mai-array/UC2-Custom-Build-for-Fluorescence-In-Incubator-Imaging/Diagrams/LightPath.jpg

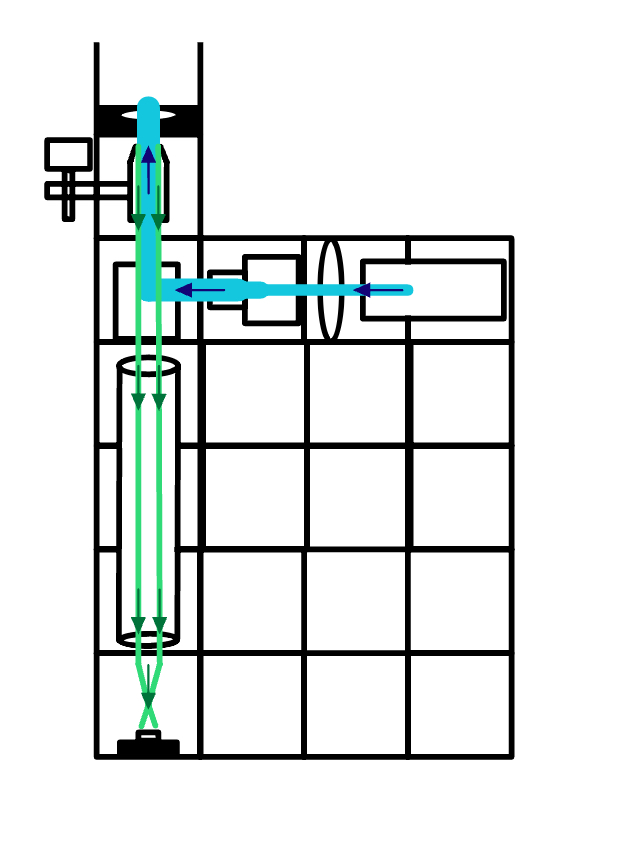
Diagrams/LightPath.jpg
