mai-array/UC2-Custom-Build-for-Fluorescence-In-Incubator-Imaging/Image Collections/Data Collection 1/auto_2025-11-21_13-37-24.jpg

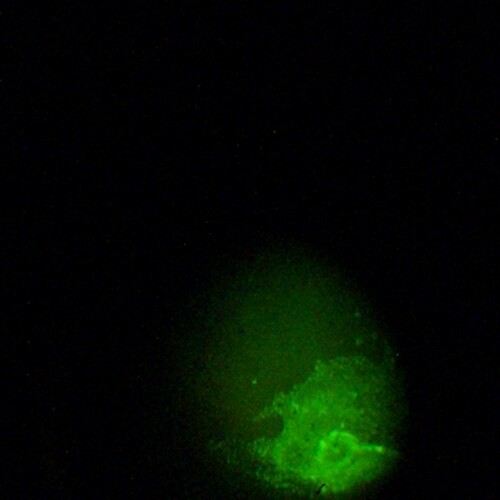
Image Collections/Data Collection 1/auto_2025-11-21_13-37-24.jpg
