mai-array/UC2-Custom-Build-for-Fluorescence-In-Incubator-Imaging/Module Pictures/beamexpander.jpg

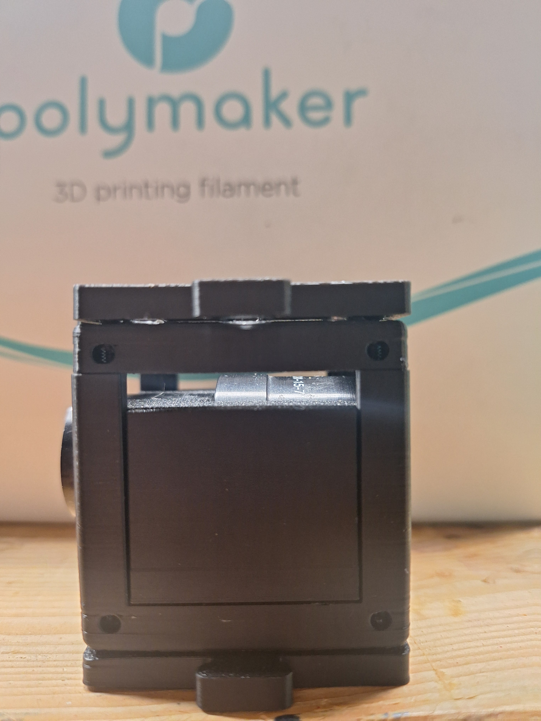
Module Pictures/beamexpander.jpg
