mai-array/UC2-Custom-Build-for-Fluorescence-In-Incubator-Imaging/Module Pictures/dichroic_beamsplitter.jpg

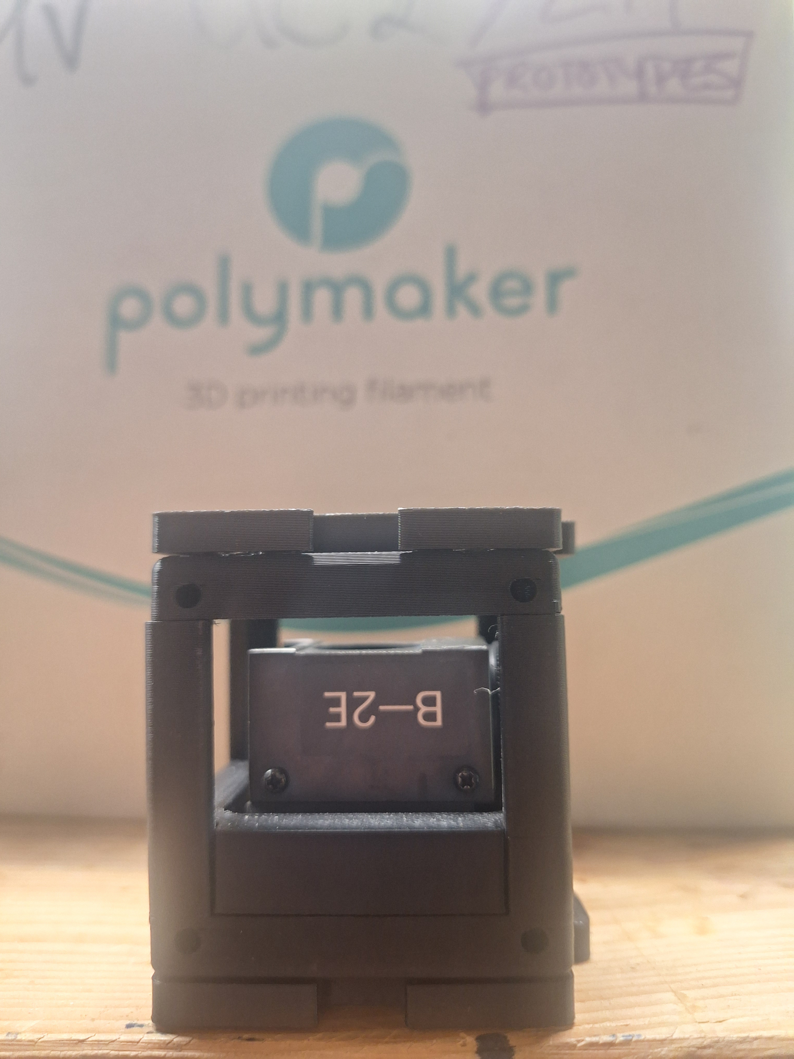
Module Pictures/dichroic_beamsplitter.jpg
