mai-array/UC2-Custom-Build-for-Fluorescence-In-Incubator-Imaging/Module Pictures/nd_filter.jpg

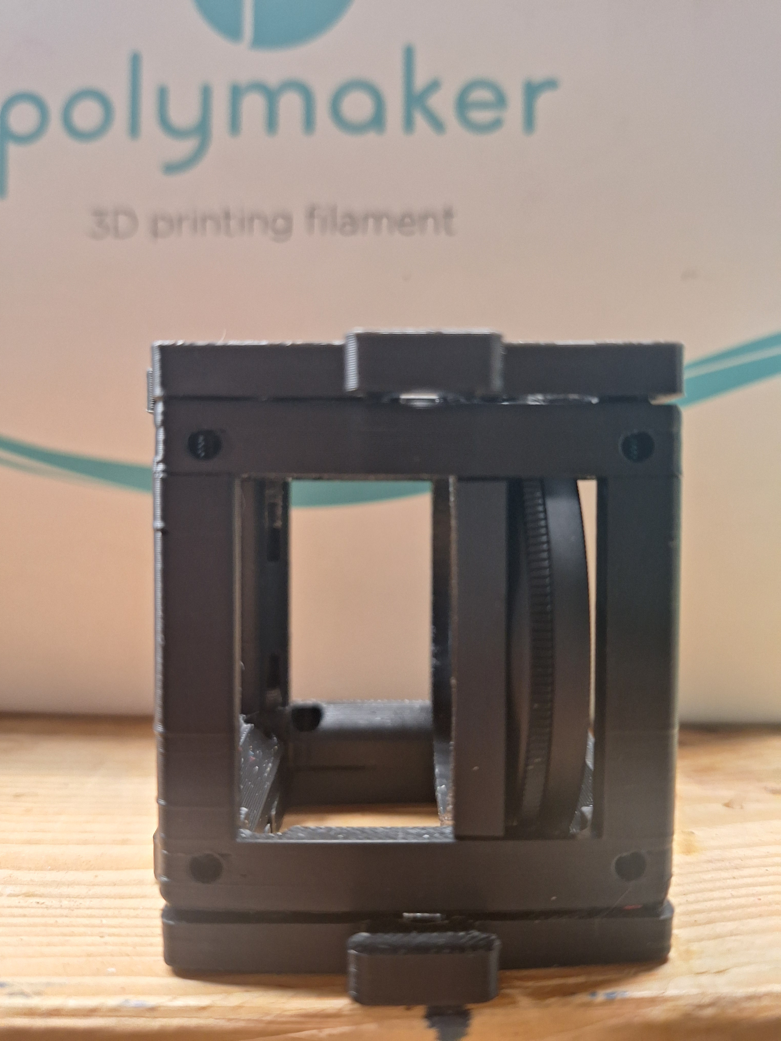
Module Pictures/nd_filter.jpg
