mai-array/UC2-Custom-Build-for-Fluorescence-In-Incubator-Imaging/Module Pictures/raspi_camera.jpg

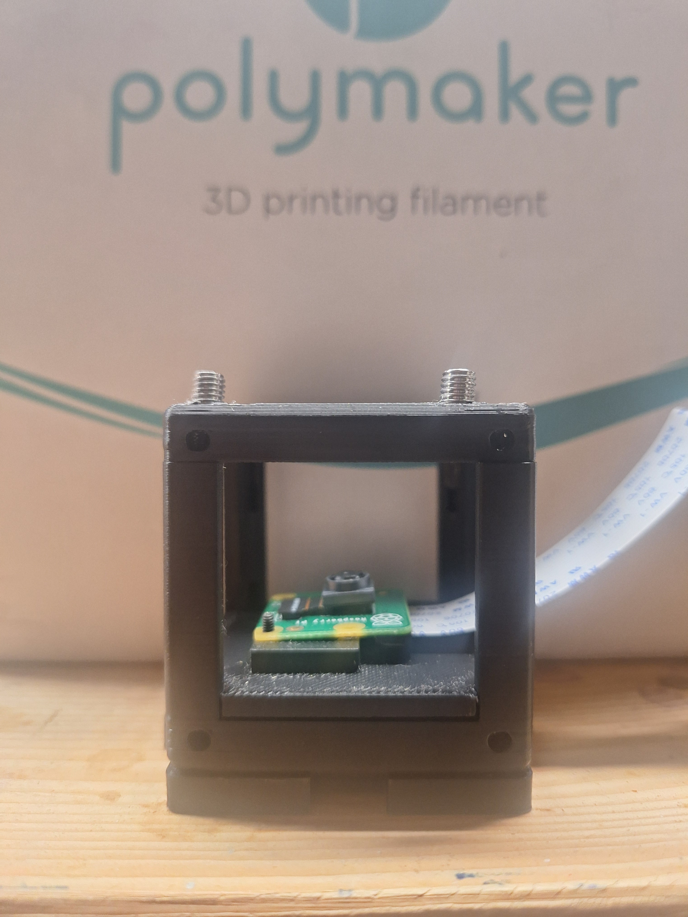
Module Pictures/raspi_camera.jpg
