mai-array/UC2-Custom-Build-for-Fluorescence-In-Incubator-Imaging/Module Pictures/tube_lens.jpg

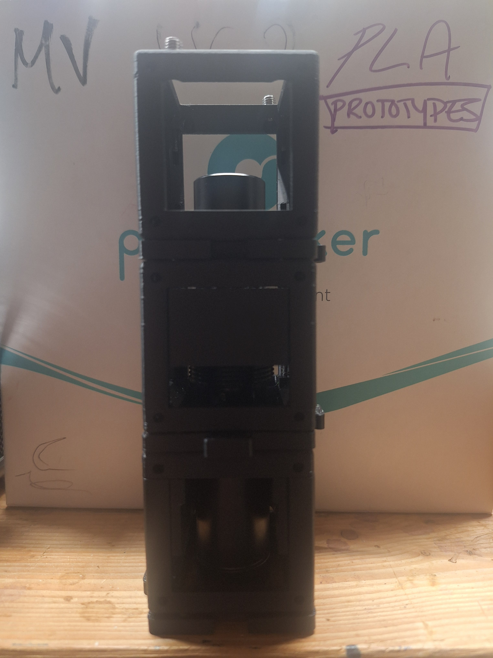
Module Pictures/tube_lens.jpg
