mai-array/UC2-Custom-Build-for-Fluorescence-In-Incubator-Imaging/Module Pictures/uc2_cube.jpg

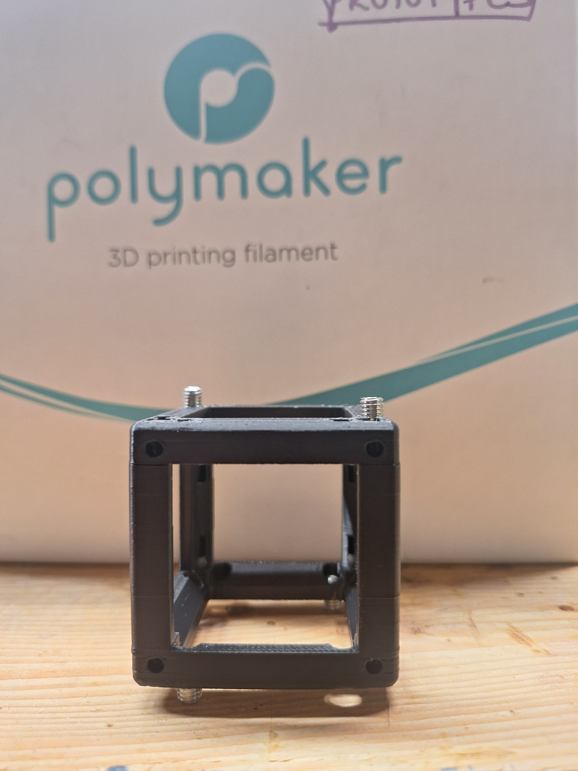
Module Pictures/uc2_cube.jpg
