mai-array/UC2-Custom-Build-for-Fluorescence-In-Incubator-Imaging/Diagrams/WiringDiagram.png

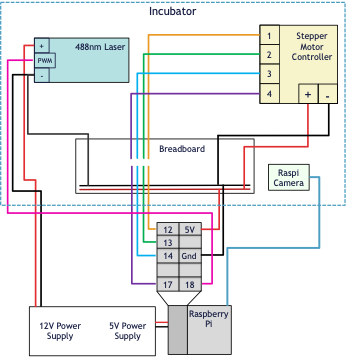
Diagrams/WiringDiagram.png
