mai-array/UC2-Custom-Build-for-Fluorescence-In-Incubator-Imaging/Full Microscope Tests/full_setup.jpg

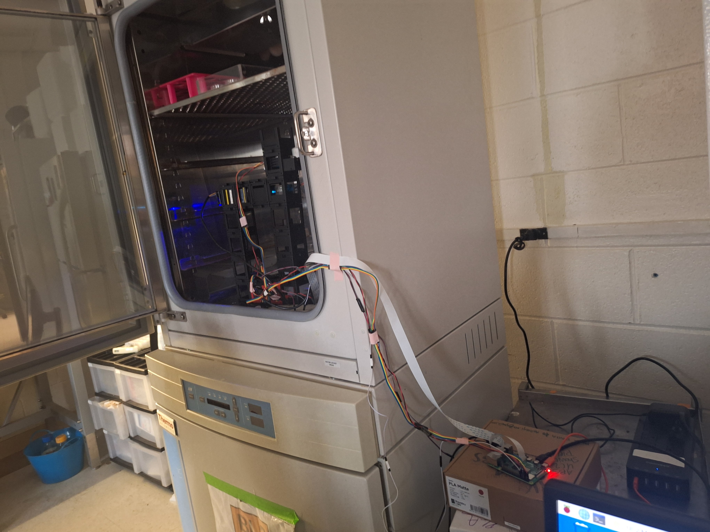
Full Microscope Tests/full_setup.jpg
