mai-array/UC2-Custom-Build-for-Fluorescence-In-Incubator-Imaging/Full Microscope Tests/in_incubator2.jpg

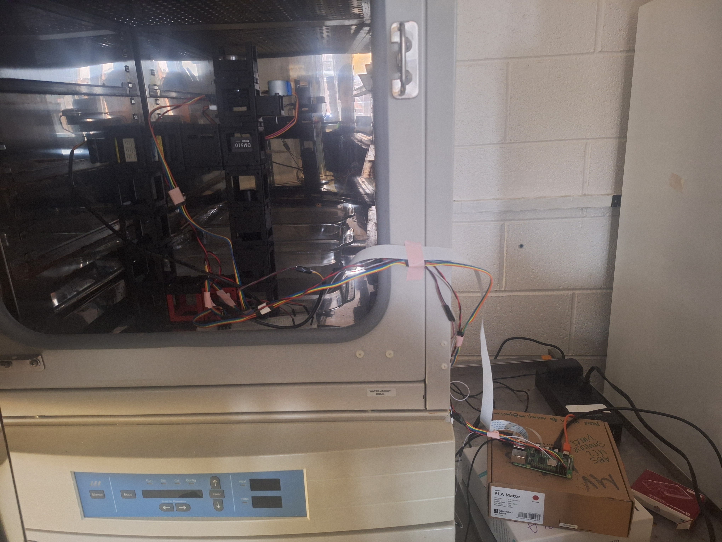
Full Microscope Tests/in_incubator2.jpg
