mai-array/UC2-Custom-Build-for-Fluorescence-In-Incubator-Imaging/Image Collections/Focusing Tests/focusTest1/focusTest15.jpg

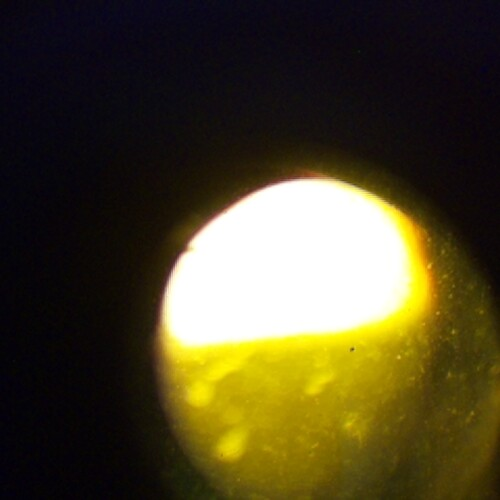
Image Collections/Focusing Tests/focusTest1/focusTest15.jpg
