mai-array/UC2-Custom-Build-for-Fluorescence-In-Incubator-Imaging/Image Collections/In-Incubator Testing/ECZTEST1/ECZIncubatorTest1.jpg

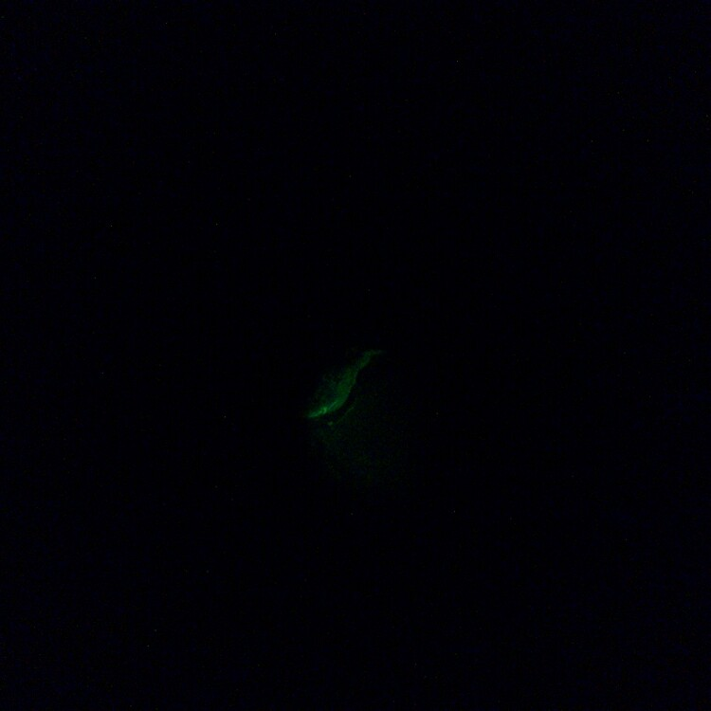
Image Collections/In-Incubator Testing/ECZTEST1/ECZIncubatorTest1.jpg
