mai-array/UC2-Custom-Build-for-Fluorescence-In-Incubator-Imaging/Image Collections/Infinity Tests/1st Infinity Test/infinityTest2.jpg

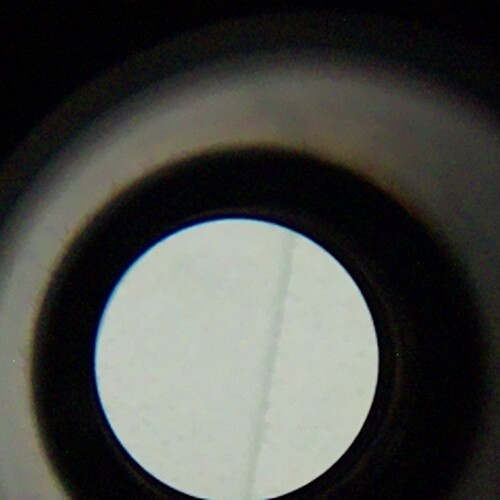
Image Collections/Infinity Tests/1st Infinity Test/infinityTest2.jpg
