mai-array/UC2-Custom-Build-for-Fluorescence-In-Incubator-Imaging/Image Collections/Infinity Tests/2nd Infinity Test/infinityTestV2_1.jpg

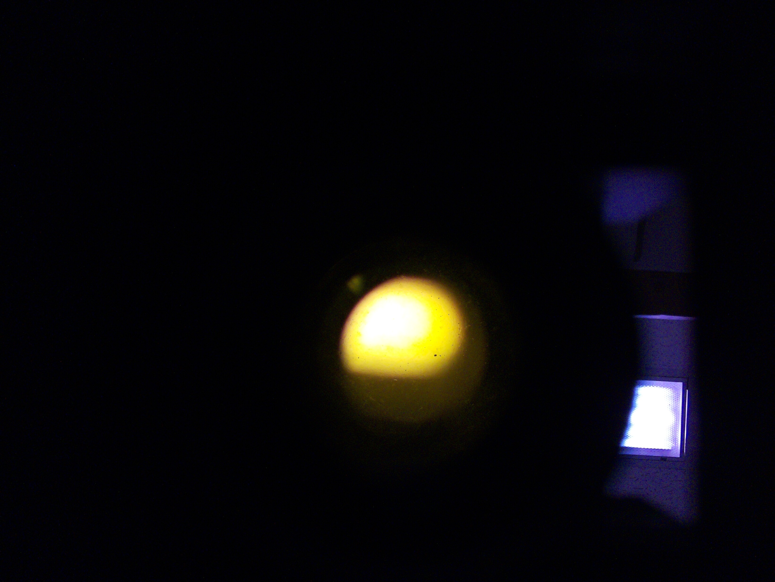
Image Collections/Infinity Tests/2nd Infinity Test/infinityTestV2_1.jpg
