mai-array/UC2-Custom-Build-for-Fluorescence-In-Incubator-Imaging/Image Collections/Infinity Tests/3rd Infinity Test/infinityTestV3_1.jpg

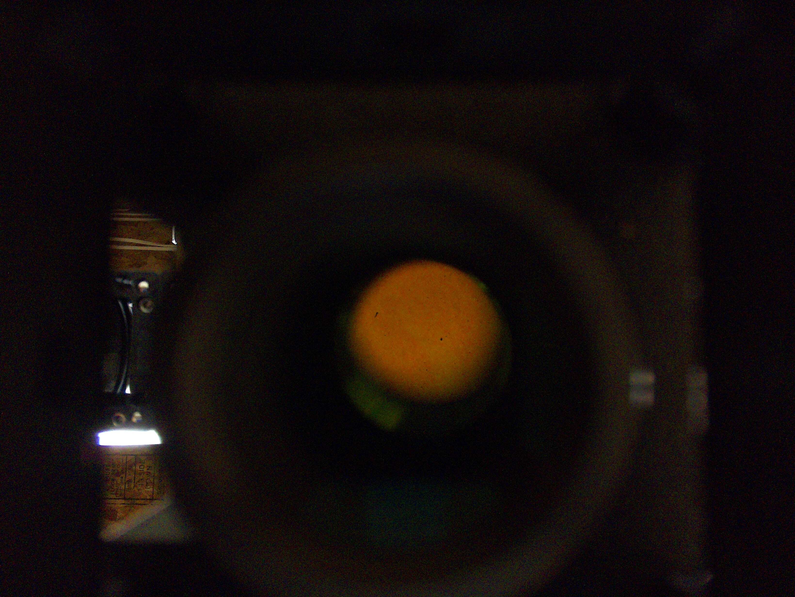
Image Collections/Infinity Tests/3rd Infinity Test/infinityTestV3_1.jpg
