mai-array/UC2-Custom-Build-for-Fluorescence-In-Incubator-Imaging/Image Collections/Initial Attempts/1st Look/noMirrorTest.jpg

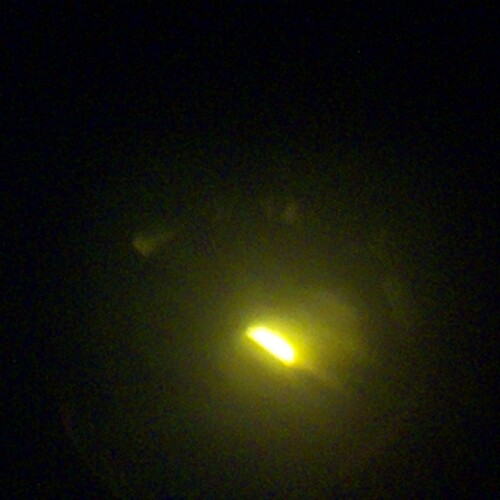
Image Collections/Initial Attempts/1st Look/noMirrorTest.jpg
