mai-array/UC2-Custom-Build-for-Fluorescence-In-Incubator-Imaging/Image Collections/Initial Attempts/PreIncTest/PreIncTest8.jpg

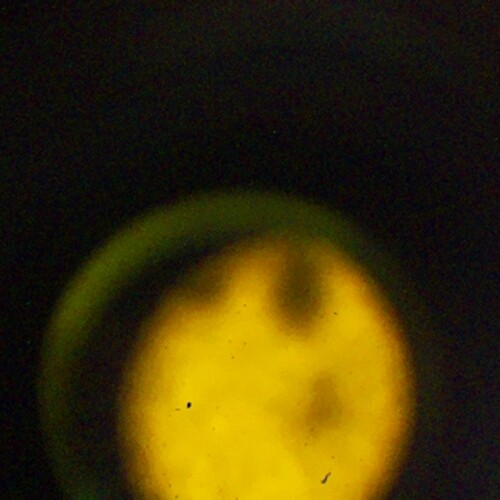
Image Collections/Initial Attempts/PreIncTest/PreIncTest8.jpg
