mai-array/UC2-Custom-Build-for-Fluorescence-In-Incubator-Imaging/Module Pictures/488nm_laser.jpg

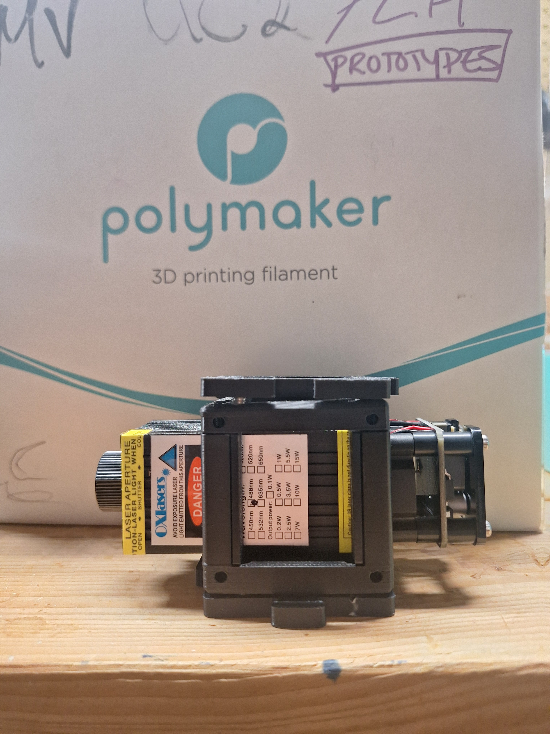
Module Pictures/488nm_laser.jpg
