mai-array/UC2-Custom-Build-for-Fluorescence-In-Incubator-Imaging/Module Pictures/objective_zstepper.jpg

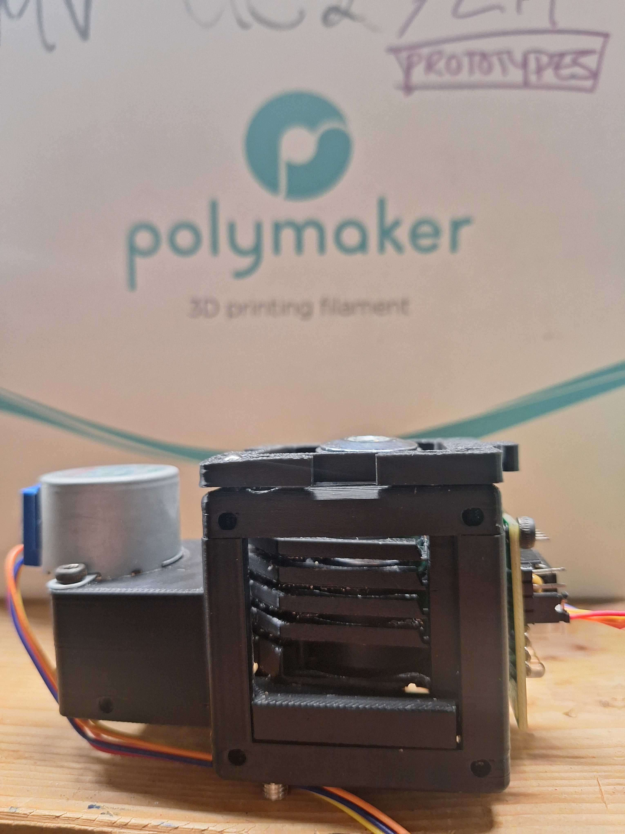
Module Pictures/objective_zstepper.jpg
