mai-array/UC2-Custom-Build-for-Fluorescence-In-Incubator-Imaging/Full Microscope Tests/microscrope_on_table.jpg

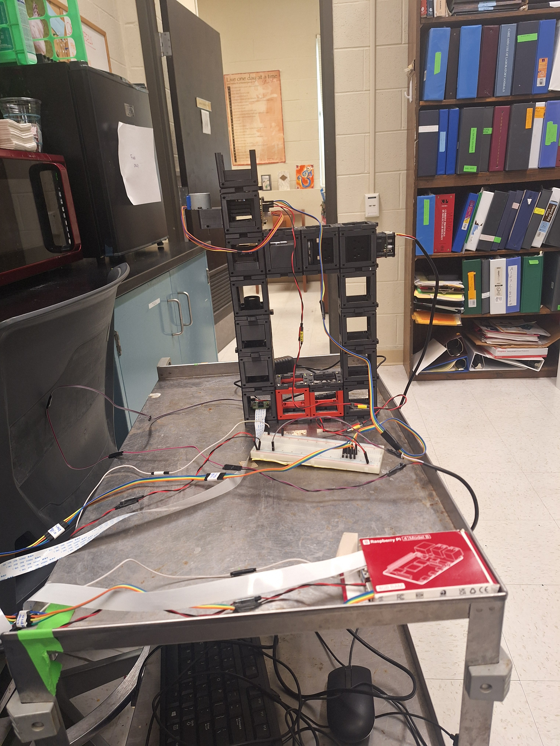
Full Microscope Tests/microscrope_on_table.jpg
